tadgeobrien/Hive-Monitor/ProgressPics/20220801_100202.jpg

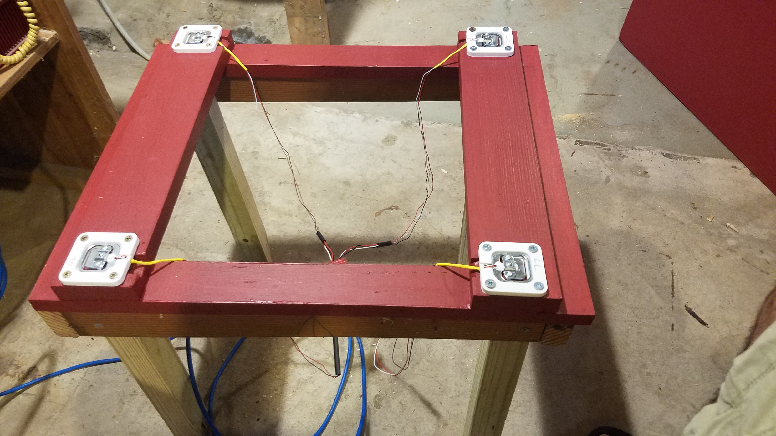
ProgressPics/20220801_100202.jpg
