tadgeobrien/Hive-Monitor/Likely_Junk/OpenLog-version/OpenLog-version.ino

/*
  An I2C based datalogger - Like the OpenLog but for I2C
  By: Nathan Seidle
  SparkFun Electronics
  Date: February 2nd, 2018
  License: This code is public domain but you buy me a beer if you use this and we meet someday (Beerware license).

  This example shows how to read the firmware version of Qwiic OpenLog.
  
  This is helpful when getting support. We will be adding features as we go and having the firmware
  version will let us know what features your board supports.
*/

#include <Wire.h>
#include "SparkFun_Qwiic_OpenLog_Arduino_Library.h"
OpenLog myLog; //Create instance

int ledPin = LED_BUILTIN; //Status LED connected to digital pin 13

void setup()
{
  pinMode(ledPin, OUTPUT);

  Wire.begin();
  myLog.begin();

  Serial.begin(9600);
  Serial.print("Qwiic OpenLog Version: ");
  Serial.println(myLog.getVersion());

  Serial.println("Done!");
}

void loop()
{
  //Blink the Status LED because we're done!
  digitalWrite(ledPin, HIGH);
  delay(1000);
  digitalWrite(ledPin, LOW);
  delay(1000);
}
